recantha/picopicorder/Colours.py

class Colours:
    def __init__(self):
        self.WHITE  = 0xFFFFFF
        self.YELLOW = 0xFFFF00
        self.RED    = 0xFF0000
        self.GREEN  = 0x00FF00
        self.BLUE   = 0x0000FF
        self.BLACK  = 0x000000
        self.ORANGE = 0xFF8811
        self.CYAN   = 0x00FFFF
        self.VIOLET = 0x9900FF
        self.GRAY   = 0x444455
        self.PURPLE = 0xAA0088
